iolo/a2e-usb-kbd/hardware/a2e-usb-kbd.kicad_sch

## KiCad design hardware/a2e-usb-kbd.kicad_sch (2026-02-07)

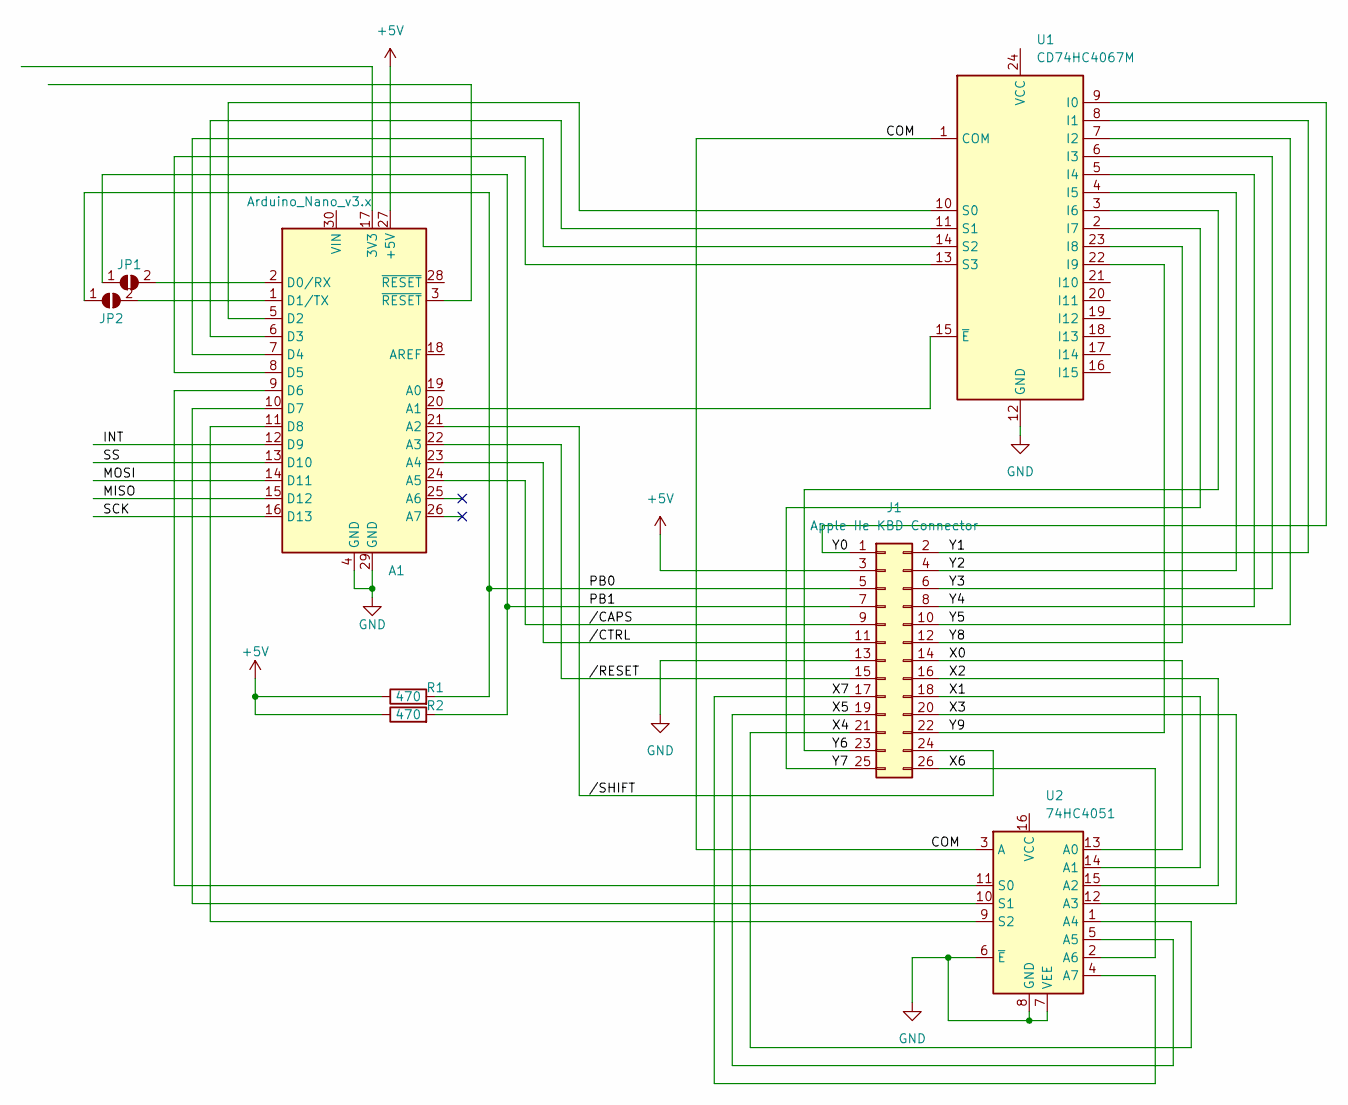
[picture p5: schematic a2e-usb-kbd.kicad_sch]

Parts:
A1: Arduino_Nano_v3.x; Arduino_Nano
J1: Apple IIe KBD Connector
JP1, JP2: SolderJumper_2_Open
R1, R2: 470
U1: CD74HC4067M; SOIC-24W_7.5x15.4mm_P1.27mm
U2: 74HC4051

Connections:
+5V: A1.27 (+5V), J1.3, R1.1, R2.1
COM: U1.1 (COM), U2.3 (A)
GND: A1.4 (GND), A1.29 (GND), J1.13, U1.12 (GND), U2.6 (~E), U2.7 (VEE), U2.8 (GND)
INT: A1.12 (D9)
MISO: A1.15 (D12)
MOSI: A1.14 (D11)
unnamed: A1.1 (D1/TX), JP2.2 (B)
unnamed: A1.2 (D0/RX), JP1.2 (B)
unnamed: A1.5 (D2), U1.10 (S0)
unnamed: A1.6 (D3), U1.11 (S1)
unnamed: A1.7 (D4), U1.14 (S2)
unnamed: A1.8 (D5), U1.13 (S3)
unnamed: A1.9 (D6), U2.11 (S0)
unnamed: A1.10 (D7), U2.10 (S1)
unnamed: A1.11 (D8), U2.9 (S2)
unnamed: A1.20 (A1), U1.15 (~E)
PB0: J1.5, JP2.1 (A), R1.2
PB1: J1.7, JP1.1 (A), R2.2
SCK: A1.16 (D13)
SS: A1.13 (D10)
X0: J1.14, U2.13 (A0)
X1: J1.18, U2.14 (A1)
X2: J1.16, U2.15 (A2)
X3: J1.20, U2.12 (A3)
X4: J1.21, U2.1 (A4)
X5: J1.19, U2.5 (A5)
X6: J1.26, U2.2 (A6)
X7: J1.17, U2.4 (A7)
Y0: J1.1, U1.9 (I0)
Y1: J1.2, U1.8 (I1)
Y2: J1.4, U1.4 (I5)
Y3: J1.6, U1.6 (I3)
Y4: J1.8, U1.5 (I4)
Y5: J1.10, U1.7 (I2)
Y6: J1.23, U1.3 (I6)
Y7: J1.25, U1.2 (I7)
Y8: J1.12, U1.23 (I8)
Y9: J1.22, U1.22 (I9)
/CAPS: A1.24 (A5), J1.9
/CTRL: A1.23 (A4), J1.11
/RESET: A1.22 (A3), J1.15
/SHIFT: A1.21 (A2), J1.24
